jihlenburg/charcoal/output/FEM/plots/trough_bulge_current_open.png

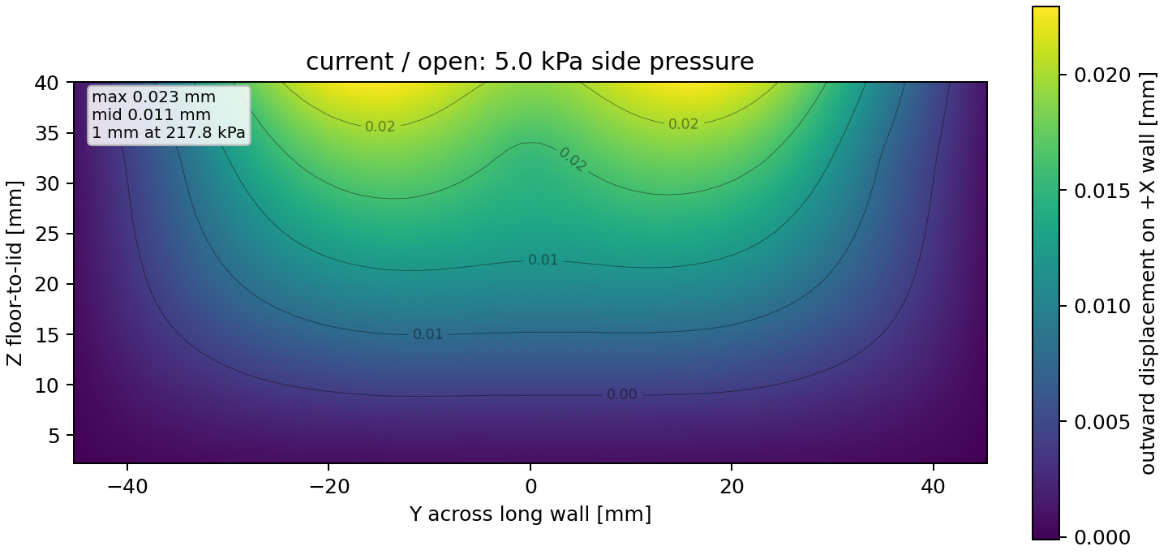
output/FEM/plots/trough_bulge_current_open.png
