jihlenburg/charcoal/output/FEM/plots/trough_bulge_plain_open.png

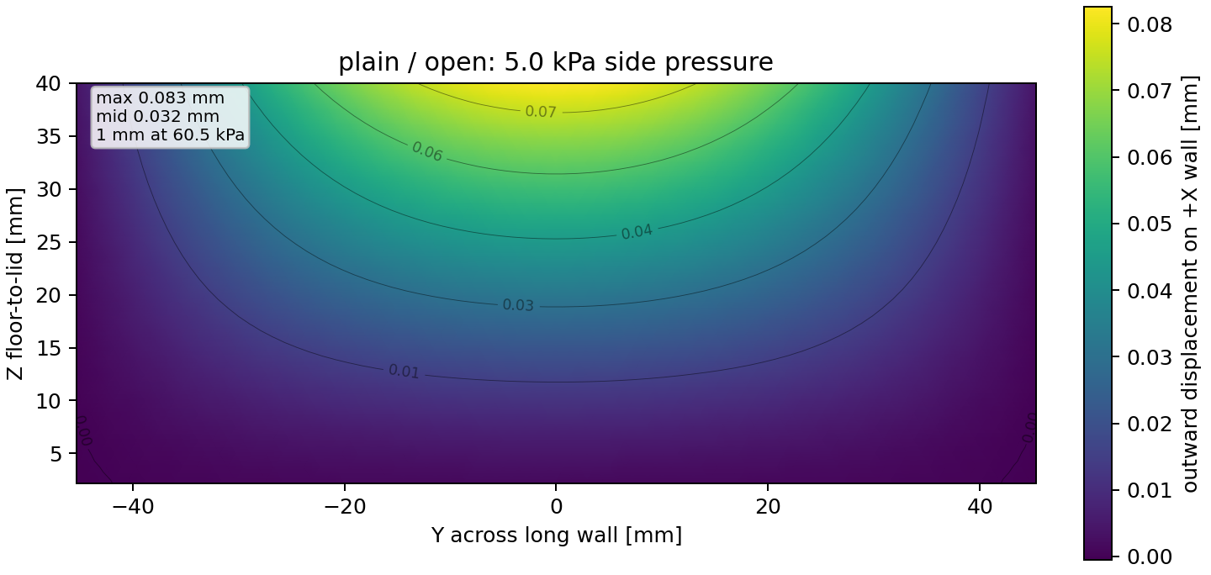
output/FEM/plots/trough_bulge_plain_open.png
